Artilect-FabTronic/Arduino-Maker-Artilect-ESP32-Board/CAO-KiCad-AMA-ESP32-Board/CAO-KiCad-AMA-ESP32-Board.png

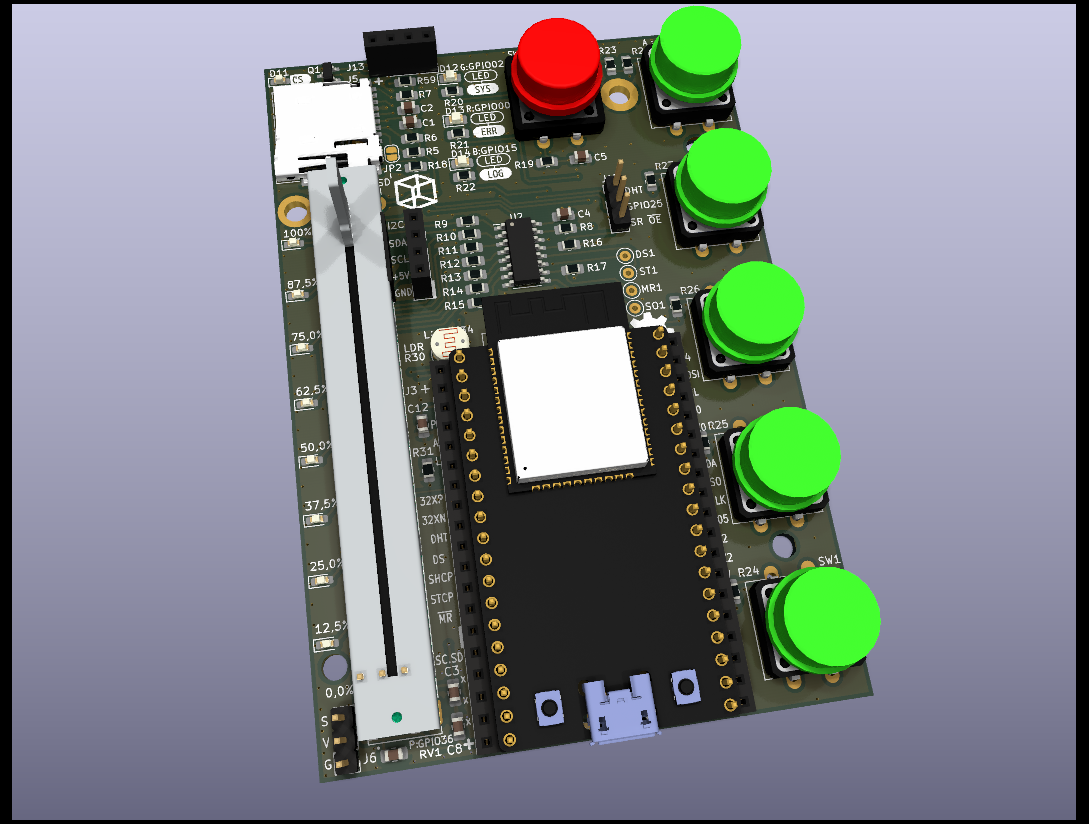
CAO-KiCad-AMA-ESP32-Board/CAO-KiCad-AMA-ESP32-Board.png
