Artilect-FabTronic/Arduino-Maker-Artilect-ESP32-Board/CAO-KiCad-AMA-ESP32-Board/doc-esp32-flash-pins-should-not-be-used.png

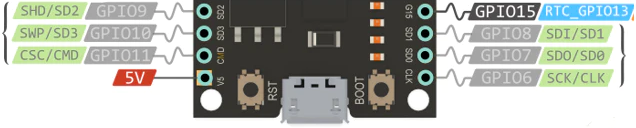
CAO-KiCad-AMA-ESP32-Board/doc-esp32-flash-pins-should-not-be-used.png
