Artilect-FabTronic/Arduino-Maker-Artilect-ESP32-Board/CAO-KiCad-AMA-ESP32-Board/local-packages3d/PrtScr capture_14.png

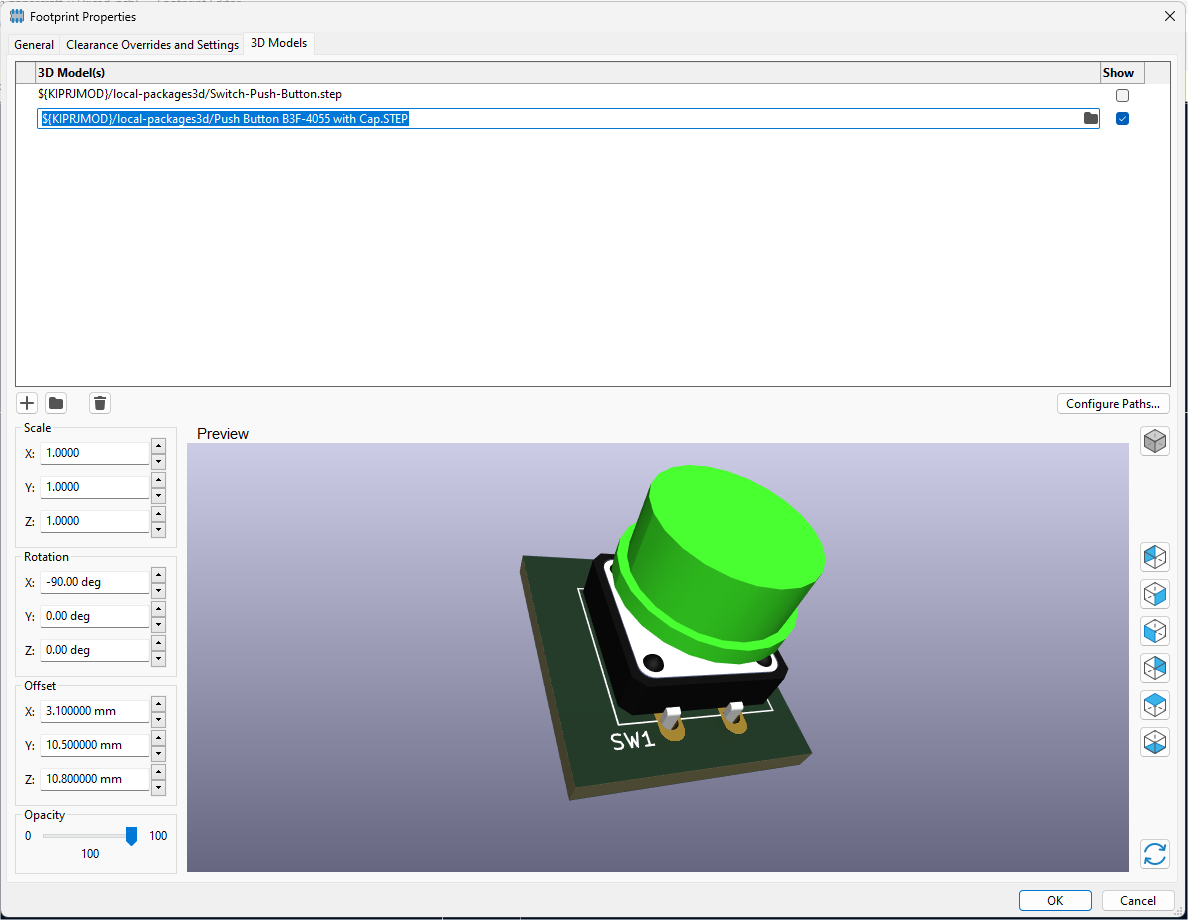
CAO-KiCad-AMA-ESP32-Board/local-packages3d/PrtScr capture_14.png
