Artilect-FabTronic/Arduino-Maker-Artilect-ESP32-Board/Images/Carte-AMA-ESP32.png

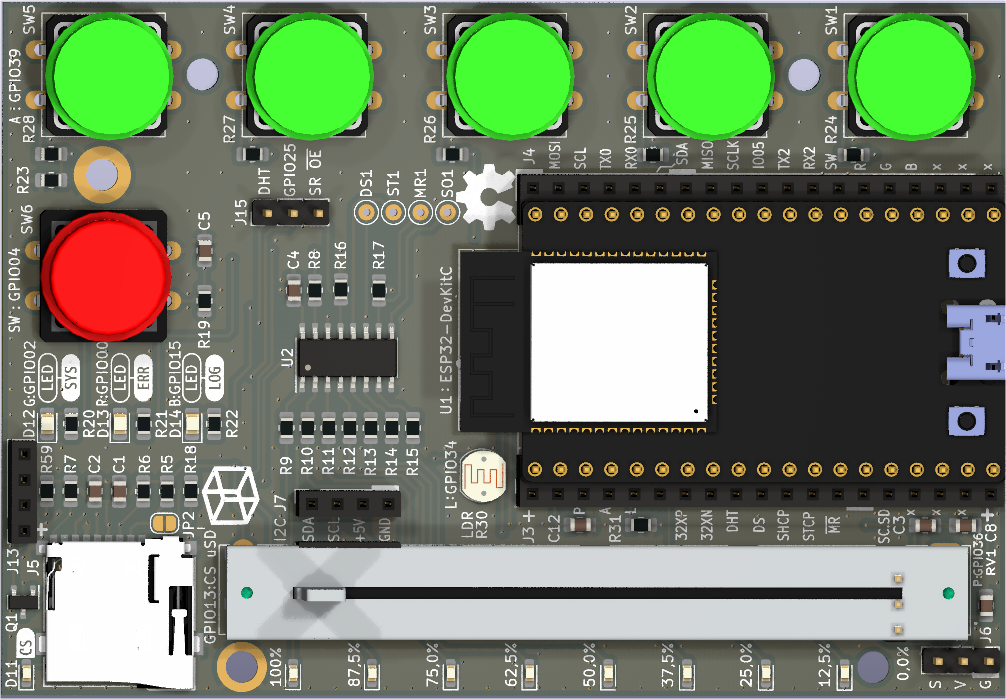
Images/Carte-AMA-ESP32.png
