Artilect-FabTronic/Arduino-Maker-Artilect-ESP32-Board/Images/gestionaire-de-carte-esp32.png

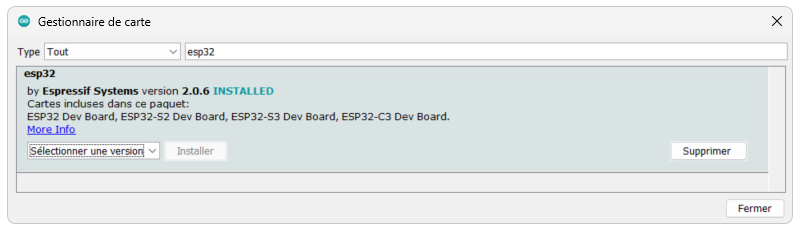
Images/gestionaire-de-carte-esp32.png
