Artilect-FabTronic/Arduino-Maker-Artilect-ESP32-Board/Images/montage-des-comopsants-02.jpg

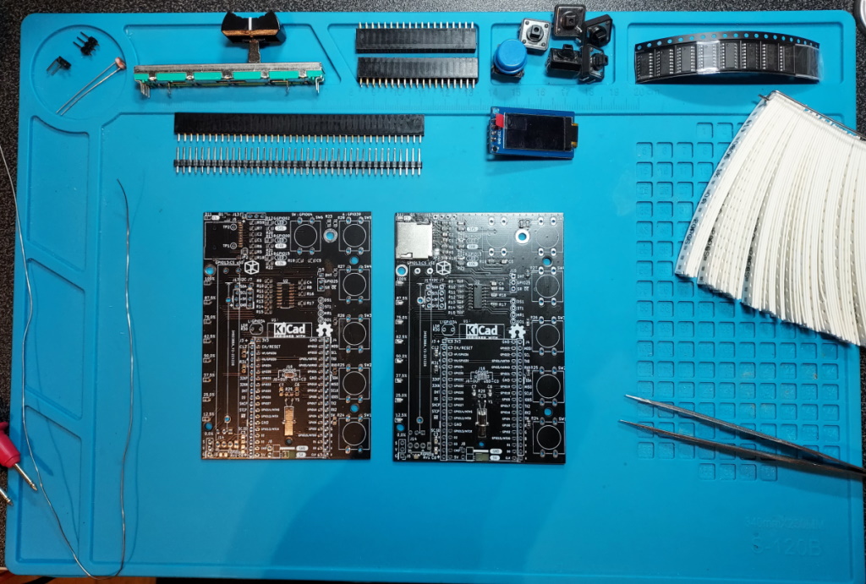
Images/montage-des-comopsants-02.jpg
